weberel/communication-module/tools/tb_export_PCB-test-rig_20260905_1100.csv

ts_ms | ts_utc | key | value
1788560165000 | 2026-09-04 22:16:05 | motion | 0
1788560479000 | 2026-09-04 22:21:19 | motion | 0
1788560671000 | 2026-09-04 22:24:31 | motion | 0
1788560967000 | 2026-09-04 22:29:27 | motion | 0
1788435204000 | 2026-09-03 11:33:24 | reset_reason | 8
1788479013000 | 2026-09-03 23:43:33 | reset_reason | 8
1788522890000 | 2026-09-04 11:54:50 | reset_reason | 8
1788555127000 | 2026-09-04 20:52:07 | reset_reason | 8
1788555490000 | 2026-09-04 20:58:10 | reset_reason | 8
1788557357000 | 2026-09-04 21:29:17 | reset_reason | 11
1788557384000 | 2026-09-04 21:29:44 | reset_reason | 8
1788557638000 | 2026-09-04 21:33:58 | reset_reason | 11
1788558888000 | 2026-09-04 21:54:48 | reset_reason | 11
1788559529000 | 2026-09-04 22:05:29 | reset_reason | 11
1788559864000 | 2026-09-04 22:11:04 | reset_reason | 11
1788560502000 | 2026-09-04 22:21:42 | reset_reason | 11
1788560693000 | 2026-09-04 22:24:53 | reset_reason | 8
1788560986000 | 2026-09-04 22:29:46 | reset_reason | 8
1788598165000 | 2026-09-05 08:49:25 | reset_reason | 8
1788426217000 | 2026-09-03 09:03:37 | solar | 0
1788426521000 | 2026-09-03 09:08:41 | solar | 0
1788426825000 | 2026-09-03 09:13:45 | solar | 0
1788427128000 | 2026-09-03 09:18:48 | solar | 0
1788427432000 | 2026-09-03 09:23:52 | solar | 0
1788427736000 | 2026-09-03 09:28:56 | solar | 0
1788428039000 | 2026-09-03 09:33:59 | solar | 0
1788428343000 | 2026-09-03 09:39:03 | solar | 0
1788428647000 | 2026-09-03 09:44:07 | solar | 0
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
1788550244000 | 2026-09-04 19:30:44 | sensor_ok | 63
1788550547000 | 2026-09-04 19:35:47 | sensor_ok | 63
1788550851000 | 2026-09-04 19:40:51 | sensor_ok | 63
1788551155000 | 2026-09-04 19:45:55 | sensor_ok | 63
1788551458000 | 2026-09-04 19:50:58 | sensor_ok | 63
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
