weberel/communication-module/tools/tb_export_PCB-test-rig_20260906_1107.csv

ts_ms | ts_utc | key | value
1788560165000 | 2026-09-04 22:16:05 | motion | 0
1788560479000 | 2026-09-04 22:21:19 | motion | 0
1788560671000 | 2026-09-04 22:24:31 | motion | 0
1788560967000 | 2026-09-04 22:29:27 | motion | 0
1788561179000 | 2026-09-04 22:32:59 | motion | 1
1788561180000 | 2026-09-04 22:33:00 | motion | 1
1788561181000 | 2026-09-04 22:33:01 | motion | 1
1788561183000 | 2026-09-04 22:33:03 | motion | 1
1788561484000 | 2026-09-04 22:38:04 | motion | 0
1788561785000 | 2026-09-04 22:43:05 | motion | 0
1788562086000 | 2026-09-04 22:48:06 | motion | 0
1788562387000 | 2026-09-04 22:53:07 | motion | 0
1788562688000 | 2026-09-04 22:58:08 | motion | 0
1788562989000 | 2026-09-04 23:03:09 | motion | 0
1788563290000 | 2026-09-04 23:08:10 | motion | 0
1788563590000 | 2026-09-04 23:13:10 | motion | 0
1788563891000 | 2026-09-04 23:18:11 | motion | 0
1788564192000 | 2026-09-04 23:23:12 | motion | 0
1788564493000 | 2026-09-04 23:28:13 | motion | 0
1788564793000 | 2026-09-04 23:33:13 | motion | 0
1788565094000 | 2026-09-04 23:38:14 | motion | 0
1788565395000 | 2026-09-04 23:43:15 | motion | 0
1788565696000 | 2026-09-04 23:48:16 | motion | 0
1788565997000 | 2026-09-04 23:53:17 | motion | 0
1788566297000 | 2026-09-04 23:58:17 | motion | 0
1788566598000 | 2026-09-05 00:03:18 | motion | 0
1788566899000 | 2026-09-05 00:08:19 | motion | 0
1788567200000 | 2026-09-05 00:13:20 | motion | 0
1788567501000 | 2026-09-05 00:18:21 | motion | 0
1788567802000 | 2026-09-05 00:23:22 | motion | 0
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
1788652167000 | 2026-09-05 23:49:27 | solar | 0
1788652469000 | 2026-09-05 23:54:29 | solar | 0
1788652770000 | 2026-09-05 23:59:30 | solar | 0
1788653072000 | 2026-09-06 00:04:32 | solar | 0
1788653373000 | 2026-09-06 00:09:33 | solar | 0
1788653674000 | 2026-09-06 00:14:34 | solar | 0
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
