weberel/communication-module/idf/src/uplink.c

#include "uplink.h"
#include "config.h"
#include "record.h"

#include <string.h>
#include <strings.h>
#include <stdio.h>
#include <stdlib.h>
#include <time.h>
#include <sys/time.h>

#include "esp_log.h"
#include "esp_timer.h"
#include "driver/uart.h"
#include "bq25792.h"
#include "nvs_flash.h"
#include "esp_event.h"
#include "esp_netif.h"
#include "esp_netif_sntp.h"
#include "esp_wifi.h"
#include "esp_http_client.h"
#include "esp_modem_api.h"
#include "mqtt_client.h"
#include "driver/gpio.h"
#include "esp_task_wdt.h"
#include "esp_ota_ops.h"
#include "esp_pm.h"   /* reproduction experiment 2026-09-14 */
#include "freertos/FreeRTOS.h"
#include "freertos/task.h"
#include "freertos/event_groups.h"

#include "board.h"
#include "secrets.h"
#include "gasflow.h"
#include "uss_link.h"
#include "devcfg.h"
#include "ota.h"

#include <math.h>

static const char *TAG = "uplink";

/* Session stopwatch. Zeroed when the modem rail comes up, so every phase
 * number below is directly comparable across sessions and across firmware
 * versions -- and reads as elapsed modem-on time, which is what costs. */
static int64_t s_sess_t0;
static uint32_t sess_ms(void)
{
    return (uint32_t)((esp_timer_get_time() - s_sess_t0) / 1000);
}

/* ISRG Root X1 CA, compiled in from isrg_cert.c (generated from the PEM). */
extern const char isrg_root_pem[];
#define isrg_root_pem_start isrg_root_pem

/* ---- timeouts / policy ---- */
#define MODEM_UART_TX        20
#define MODEM_UART_RX        21

/* Link speed to the A7672.
 *
 * START is what the modem is guaranteed to answer on after a power cycle;
 * AT+IPR is volatile on SIMCom, so every session begins here.
 * FAST is the target once we are talking. 921600 needs R405-R408 at 2.2 k --
 * with the stock 10 k level-shifter pull-ups 230400 is the ceiling and 460800
 * is dead (testing-status.md). Lower FAST to 230400 on an un-reworked board. */
/* Upper bound on how long we wait for the modem to answer AT after PWRKEY.
 * Generous on purpose -- this is a ceiling, not a delay: the poll exits as soon
 * as the modem replies, so a slow boot costs only what it actually costs. */
#define MODEM_READY_TO_MS    15000

#define MODEM_BAUD_START     115200
/* DISABLED (set equal to START) after a measured failure, 2026-09-21.
 *
 * TRIED: 921600, which testing-status.md says this unit's reworked 2.2 k
 * level-shifter pull-ups support. RESULT: "did not stick", and the session then
 * failed at REGISTRATION (reg=0) having burned 37.6 s.
 *
 * WHY THE FALLBACK BELOW CANNOT WORK. AT+IPR SUCCEEDS -- the modem moves to the
 * new rate. If our own re-sync then fails, dropping our UART back to 115200
 * leaves the modem at 921600, i.e. mismatched in the one direction that cannot
 * be talked out of: commanding it back needs the link that is broken. Only a
 * rail power-cycle recovers it, which is why the whole session was lost.
 *
 * AND IT WAS NEVER THE BOTTLENECK. One batch is 8 records ~7 KB = 0.6 s at
 * 115200, yet the measured failure was n_batch=0 with an 18.4 s drain: the
 * first publish transmitted fine and then waited for an ACK that never came.
 * The session's cost is TIMEOUTS (publish 20 s, reconnect 15 s, teardown 18.5 s,
 * modem boot 8.9 s), not throughput. Raise this only with a re-sync that is
 * retried at BOTH rates before giving up, and only if throughput is ever shown
 * to bind. */
#define MODEM_BAUD_FAST      115200
#define ATTACH_TIMEOUT_S     45      /* normal attach budget */
#define ATTACH_DEEP_S        180     /* once-a-day deep search */
#define NO_SIGNAL_FAILFAST_S 25      /* CSQ still 99 after this -> abort attempt */
#define MQTT_CONNECT_TO_MS   30000
#define PUBLISH_TO_MS        20000
/* Back to 8 after the telemetry trim: 22 datapoints per record x 8 = ~176 per
 * publish, comfortably under what made ThingsBoard Cloud drop the connection
 * (that was ~320, at 40 datapoints x 8). Larger batches drain a backlog in
 * fewer round trips, which matters over a slow cellular link. */
#define BATCH_RECORDS        8
#define BATCH_GAP_MS         400     /* ThingsBoard Cloud dislikes bursts */

#define CLOCK_MIN 1767225600L        /* 2026-01-01 */
#define CLOCK_MAX 2082758400L        /* 2036-01-01 */

static bool clock_valid(void)
{
    time_t t = time(NULL);
    return t >= CLOCK_MIN && t < CLOCK_MAX;
}

/* ===================== MQTT publisher (transport-agnostic) ===================== */

static EventGroupHandle_t s_ev;
#define EV_MQTT_UP   BIT0
#define EV_MQTT_FAIL BIT1
#define EV_PUBACK    BIT2
#define EV_IP_UP     BIT3
#define EV_CFG_DONE  BIT4   /* config topic answered: payload, or the subscribe was refused */

static esp_mqtt_client_handle_t s_mqtt;
static volatile int s_pending_msg_id = -1;

/* ---- downlink: retained config (com-0.35, DOWNLINK.md) ----------------------
 * The device may only READ ecotrace/<user>/config; the ACL refuses everything
 * else, and until the ACL is deployed the SUBSCRIBE itself is refused. Both
 * are "no config", not errors. */
#define MQTT_CFG_TOPIC   "ecotrace/" MQTT_USERNAME "/config"
#define CFG_WAIT_MS      2000      /* retained delivery follows SUBACK at once;
                                    * the wait only runs out when nothing is retained */
static volatile int s_cfg_sub_id = -1;
static volatile devcfg_rc_t s_cfg_rc;
static volatile bool s_cfg_seen;    /* a payload arrived this session */

static void mqtt_event(void *arg, esp_event_base_t base, int32_t id, void *data)
{
    esp_mqtt_event_handle_t e = data;
    switch ((esp_mqtt_event_id_t)id) {
    case MQTT_EVENT_CONNECTED:    xEventGroupSetBits(s_ev, EV_MQTT_UP);   break;
    case MQTT_EVENT_ERROR:
    case MQTT_EVENT_DISCONNECTED: xEventGroupSetBits(s_ev, EV_MQTT_FAIL); break;
    case MQTT_EVENT_PUBLISHED:
        if (e->msg_id == s_pending_msg_id) xEventGroupSetBits(s_ev, EV_PUBACK);
        break;
    case MQTT_EVENT_SUBSCRIBED:
        if (e->msg_id == s_cfg_sub_id && e->error_handle &&
            e->error_handle->error_type == MQTT_ERROR_TYPE_SUBSCRIBE_FAILED) {
            /* MQTT 5 reason code >= 0x80: not authorised (ACL not deployed
             * yet). Same as an empty topic. */
            ESP_LOGW(TAG, "config subscribe refused -- no config");
            xEventGroupSetBits(s_ev, EV_CFG_DONE);
        }
        break;
    case MQTT_EVENT_DATA:
        if (e->topic_len == (int)strlen(MQTT_CFG_TOPIC) &&
            memcmp(e->topic, MQTT_CFG_TOPIC, e->topic_len) == 0) {
            /* Payloads are a few hundred bytes, far below the client's
             * buffer, so one event carries the whole message; anything that
             * arrives fragmented is not a config we know and is dropped. */
            if (e->current_data_offset == 0 && e->total_data_len == e->data_len) {
                s_cfg_rc   = devcfg_apply(e->data, (size_t)e->data_len);
                s_cfg_seen = true;
                xEventGroupSetBits(s_ev, EV_CFG_DONE);
            }
        }
        break;
    default: break;
    }
}

static bool mqtt_up(void)
{
    esp_mqtt_client_config_t cfg = {
        .broker.address.uri = MQTT_URI,
        /* PINNED, do not touch. Let's Encrypt moved to the Generation Y root in
         * Jan 2026, so certs now chain to ISRG Root YR -- the SERVER is
         * configured to serve the chain cross-signed by X1 precisely so this
         * file keeps working. X1 is being retired eventually; pin Root YR (or
         * both) then, not now. */
        .broker.verification.certificate = isrg_root_pem_start,
        .credentials.username = MQTT_USERNAME,
        /* The secret goes in the PASSWORD field, not the username: brokers log
         * usernames on every connect. */
        .credentials.authentication.password = MQTT_PASSWORD,
        /* MQTT 5, and this is not cosmetic. On 3.1.1 a broker that REFUSES a
         * publish still returns PUBACK -- there is no not-authorised code --
         * and publish_acked() advances the flash ring cursor on PUBACK. A
         * refused publish would therefore discard records that never arrived.
         * MQTT 5 returns reason code 0x87 and the refusal becomes visible. */
        .session.protocol_ver = MQTT_PROTOCOL_V_5,
        .network.timeout_ms = 15000,
        .session.keepalive = 60,
    };
    s_mqtt = esp_mqtt_client_init(&cfg);
    if (!s_mqtt) return false;
    esp_mqtt_client_register_event(s_mqtt, ESP_EVENT_ANY_ID, mqtt_event, NULL);
    xEventGroupClearBits(s_ev, EV_MQTT_UP | EV_MQTT_FAIL);
    if (esp_mqtt_client_start(s_mqtt) != ESP_OK) return false;
    EventBits_t b = xEventGroupWaitBits(s_ev, EV_MQTT_UP | EV_MQTT_FAIL,
                                        pdTRUE, pdFALSE,
                                        pdMS_TO_TICKS(MQTT_CONNECT_TO_MS));
    return (b & EV_MQTT_UP) != 0;
}

static void mqtt_down(void)
{
    if (!s_mqtt) return;
    esp_mqtt_client_stop(s_mqtt);
    esp_mqtt_client_destroy(s_mqtt);
    s_mqtt = NULL;
}

/* Subscribe to the retained config and wait for it, at most CFG_WAIT_MS.
 * Runs BEFORE the drain so the sleep length and upload countdown computed
 * after the session already use the new values (the ack in the status
 * message is then what will actually happen). Nothing here can fail the
 * session: no payload, a refused subscribe or a rejected payload all leave
 * the NVS values in force. */
static void config_fetch(void)
{
    if (!s_mqtt) return;
    s_cfg_seen = false;
    xEventGroupClearBits(s_ev, EV_CFG_DONE);
    s_cfg_sub_id = esp_mqtt_client_subscribe(s_mqtt, MQTT_CFG_TOPIC, 1);
    if (s_cfg_sub_id < 0) { ESP_LOGW(TAG, "config subscribe not sent"); return; }
    EventBits_t b = xEventGroupWaitBits(s_ev, EV_CFG_DONE, pdTRUE, pdFALSE,
                                        pdMS_TO_TICKS(CFG_WAIT_MS));
    if (!(b & EV_CFG_DONE))
        ESP_LOGI(TAG, "no retained config within %d ms", CFG_WAIT_MS);
    else if (s_cfg_seen)
        ESP_LOGI(TAG, "config: %s (ver %lu, sample %lu s, upload %lu s)",
                 devcfg_rc_name(s_cfg_rc), (unsigned long)devcfg_ver(),
                 (unsigned long)devcfg_sample_s(), (unsigned long)devcfg_upload_s());
    esp_mqtt_client_unsubscribe(s_mqtt, MQTT_CFG_TOPIC);
}

/* ---- OTA (com-0.36, DOWNLINK.md "OTA semantics") --------------------------
 * After the drain, so the data always goes first, and before the status
 * message, so a failure is reported in the same session. On success the
 * status still carries the OLD version (the new image's first session is the
 * acknowledgement) and main.c restarts once the session is torn down.
 *
 * Only tried with a comfortable battery: the new image must complete one
 * upload session before its first deep sleep or the bootloader rolls it back,
 * and a session that is skipped for a low pack would waste the whole attempt. */
#define OTA_MIN_VBAT_MV   (MODEM_MIN_VBAT_MV + 100)
#define OTA_MAX_TRIES     3

/* This session published, so the image that is running works: tell the
 * bootloader to keep it. MUST run before ota_attempt(), and nowhere after it:
 * esp_ota_mark_app_valid_cancel_rollback() marks whichever otadata entry is
 * ACTIVE, not the partition that is running, and esp_https_ota_finish() makes
 * the freshly written slot the active entry. Marking after an OTA therefore
 * validates the NEW image before it has ever booted, and the bootloader will
 * never roll it back (found 2026-10-01: a build with a wrong broker host
 * survived every wake; the four OTAs the day before had no protection either).
 * A no-op unless this slot is PENDING_VERIFY, i.e. our own first boot after
 * an OTA. */
static void confirm_running_image(const uplink_result_t *res)
{
    if (!res->any_success) return;
    const esp_partition_t *run = esp_ota_get_running_partition();
    esp_ota_img_states_t st;
    if (run && esp_ota_get_state_partition(run, &st) == ESP_OK && st == ESP_OTA_IMG_PENDING_VERIFY) {
        esp_ota_mark_app_valid_cancel_rollback();
        ESP_LOGI(TAG, "first session after OTA published -- %s (" FW_VERSION ") marked valid", run->label);
    }
}

static void ota_attempt(const uplink_ctx_t *ctx, uplink_result_t *res)
{
    confirm_running_image(res);
    const devcfg_fw_t *t = devcfg_fw_target();
    if (!t || res->ota_ready) return;
    if (strcmp(t->ver, FW_VERSION) == 0) return;          /* already running it */
    if (ctx->vbat_mv && ctx->vbat_mv < OTA_MIN_VBAT_MV) {
        ESP_LOGW(TAG, "OTA %s deferred: VBAT %u mV < %d", t->ver, ctx->vbat_mv, OTA_MIN_VBAT_MV);
        return;
    }
    uint8_t n = devcfg_fw_tries(t->ver);
    if (n >= OTA_MAX_TRIES) {
        ESP_LOGW(TAG, "OTA %s not retried (%u attempts)", t->ver, n);
        return;
    }
    /* A version that downloaded, booted and then could not upload was rolled
     * back by the bootloader: the same bytes would fail the same way, and a
     * retry here would run BEFORE the status message and clear the very
     * fw_err the server needs to see. Stricter than the contract's three
     * attempts, on purpose. A different fw_ver lifts it. */
    if (devcfg_fw_err() && strcmp(devcfg_fw_err(), "rollback") == 0 &&
        devcfg_fw_err_ver() && strcmp(devcfg_fw_err_ver(), t->ver) == 0) {
        ESP_LOGW(TAG, "OTA %s not retried: it was rolled back", t->ver);
        return;
    }
    devcfg_fw_note_try(t->ver);                            /* counted before, so a crash counts */
    esp_task_wdt_reset();
    ota_rc_t rc = ota_run(t->ver, t->url, t->sha256);
    if (rc == OTA_OK) {
        devcfg_fw_clear_err();
        res->ota_ready = true;
    } else {
        devcfg_fw_set_err(ota_rc_name(rc), t->ver);
    }
}

/* QoS 1 publish, blocking until PUBACK -- the ring cursor only advances on ack. */
static bool publish_acked(const char *json)
{
    if (!s_mqtt) return false;
    xEventGroupClearBits(s_ev, EV_PUBACK | EV_MQTT_FAIL);
    /* Per-device topic. The broker ACL is `pattern write ecotrace/%u/telemetry`,
     * so this must match the authenticated username or the publish is refused
     * -- visibly, now that we speak MQTT 5. */
    int id = esp_mqtt_client_publish(s_mqtt, MQTT_TOPIC, json, 0, 1, 0);
    if (id < 0) return false;
    s_pending_msg_id = id;
    EventBits_t b = xEventGroupWaitBits(s_ev, EV_PUBACK | EV_MQTT_FAIL,
                                        pdTRUE, pdFALSE,
                                        pdMS_TO_TICKS(PUBLISH_TO_MS));
    return (b & EV_PUBACK) != 0;
}

/* ---- derived ultrasonic values (gasflow.c) ---------------------------------
 *
 * The server does not compute (agreed 2026-09-25), so the board sends the
 * derived set it plots: per sample c, CH4 fraction and the 0/1 flags; per
 * window the gas and METHANE volumes at standard conditions, mean flow, Re,
 * cutoff, coverage and length. The raw keys still carry every input, so a
 * refit can recompute history later; uss_derive_ver names the constants.
 * (idf-0.31 had cut this to methane only; the server asked for the rest back
 * in 0.32/0.33.)
 *
 * Computed HERE, at upload, from the raw fields already in the record, so the
 * record layout (and REC_MAGIC) stays untouched and a backlog logged before
 * this build still gets it.
 *
 * WINDOWS come from a record and its PREDECESSOR in the flash ring, read back
 * by seq -- not remembered in RAM, so it survives deep sleep, reboots and
 * sessions that start mid-backlog alike. No predecessor, no window: a missing
 * predecessor is never treated as zero. */
static void raw_of(const LogRecord *r, gf_raw_t *raw)
{
    raw->code        = r->uss_code;
    raw->tof_ups_q40 = r->uss_tof_ups_q40;
    raw->tof_dns_q40 = r->uss_tof_dns_q40;
    raw->dtof_ps     = r->uss_dtof_ps;
    raw->amp_ups     = r->uss_amp_ups;
    raw->amp_dns     = r->uss_amp_dns;
    raw->gain        = r->uss_gain;
}

/* A sample needs the module (bit 4) AND the in-line MS5837 (bit 3). */
static void sample_of(const gf_cfg_t *cfg, const LogRecord *r, gf_sample_t *s)
{
    gf_raw_t raw;
    memset(s, 0, sizeof(*s));
    if ((r->sensor_ok & 0x18) != 0x18) return;
    raw_of(r, &raw);
    gf_sample(cfg, &raw, r->press_dmbar / 10.0, r->temp_cC / 100.0, s);
}

/* Window between prev and cur. Returns NULL and fills *w on success, or a short
 * reason, which is published so a missing volume explains itself. */
static const char *window_of(const gf_cfg_t *cfg, const LogRecord *prev,
                             const LogRecord *cur, const gf_sample_t *s_cur,
                             gf_window_t *w, double *cov, uint32_t *dt_s)
{
    if (!(prev->sensor_ok & 0x10) || !(cur->sensor_ok & 0x10)) return "no_module";
    if (cur->uss_tot_flags & USS_TOT_FLAG_SAT)                 return "saturated";
    /* <= 0 also covers a totalizer reset and pre-PROTO 3 records (all zero). */
    int64_t ds0 = cur->uss_s0 - prev->uss_s0;
    int64_t ds1 = cur->uss_s1 - prev->uss_s1;
    if (ds0 <= 0)                                              return "ds0";

    /* Wall-clock window. uptime_s is only comparable within one boot epoch. */
    if (prev->ts_s && cur->ts_s > prev->ts_s)
        *dt_s = cur->ts_s - prev->ts_s;
    else if (prev->boot_id == cur->boot_id && cur->uptime_s > prev->uptime_s)
        *dt_s = cur->uptime_s - prev->uptime_s;
    else                                                       return "no_dt";

    /* Composition, P and T from this record's sample, else the predecessor's
     * (the window touches both ends). */
    gf_sample_t s_prev;
    const gf_sample_t *rep = s_cur;
    const LogRecord   *rr  = cur;
    if (!rep->ok) {
        sample_of(cfg, prev, &s_prev);
        rep = &s_prev;
        rr  = prev;
    }
    /* Kept apart on purpose: without the in-line MS5837 there is no pressure
     * or temperature, so the volume cannot be taken to standard conditions and
     * -- worse -- the CH4 fraction cannot be read from the speed of sound at
     * all (it needs the gas temperature). That is a missing sensor, not a bad
     * ultrasonic sample, and the two need different fixes. */
    if (!rep->ok && !(cur->sensor_ok & 0x08) && !(prev->sensor_ok & 0x08))
                                                               return "no_pt";
    if (!rep->ok)                                              return "no_sample";

    /* Integrated time claimed by S0, at the representative ToF, against the
     * wall clock. Above 1 means the sum claims more time than passed. Median
     * 0.990 over a day of field windows (eco-field-02, 2026-09-23).
     *
     * Not judged below 60 s: record stamps are whole seconds and are taken a
     * few seconds before the totalizer read, which alone moves a 5 s window's
     * coverage by +-50 %. The volume of a short window does not depend on dt,
     * so it is kept rather than thrown away on a check it cannot pass. */
    double tu_ns = rr->uss_tof_ups_q40 / 1099511.627776 * 1000.0;
    double td_ns = rr->uss_tof_dns_q40 / 1099511.627776 * 1000.0;
    *cov = (double) ds0 / 1099511627776.0 * tu_ns * td_ns / (*dt_s * 1000.0);
    if (*dt_s >= 60 && *cov > USS_WIN_COV_MAX)                return "coverage";

    if (!gf_window(cfg, ds1, ds0, *dt_s * 1000u, rep, w))     return "window";
    if (fabs(w->q_n_lpm) > USS_WIN_Q_MAX_LPM)                  return "q_max";
    return NULL;
}

static int derived_values(const LogRecord *r, char *out, size_t cap)
{
    gf_cfg_t cfg;
    gf_profile(&cfg, USS_GAS_PROFILE, USS_CELL);

    gf_sample_t s;
    sample_of(&cfg, r, &s);

    /* Configuration: what the server needs to recompute from the raw keys.
     * uss_validated is a property of profile + cell (always 0 on 44 mm): it is
     * what marks provisional data, so it goes on every record. */
    int n = snprintf(out, cap,
        ",\"uss_gas\":\"%s\",\"uss_cell\":%d,\"uss_derive_ver\":%d,\"uss_validated\":%u",
        gf_gas_name(cfg.kind), gf_cell_mm(cfg.cell), GF_DERIVE_VER,
        cfg.validated ? 1u : 0u);
    if (n < 0 || (size_t)n >= cap) return -1;

    /* Sample flags, sent as 0 OR 1 whenever the check actually ran, so an
     * absent key means "not evaluated", never "not set" (server request,
     * 2026-09-25). The ToF check runs on every code-122 sample with P and T;
     * the composition and the echo check only on one whose ToF passed. A
     * record without them says why through uss_code / sensor_ok. */
    if (s.ok || s.tof_bad)
        n += snprintf(out + n, cap - n, ",\"uss_tof_bad\":%u", s.tof_bad ? 1u : 0u);
    if (s.ok && n > 0 && (size_t)n < cap)
        n += snprintf(out + n, cap - n,
                      ",\"uss_c_mps\":%.2f,\"uss_x_a\":%.4f,\"uss_not_gas\":%u",
                      s.c_mps, s.x_a, s.not_gas ? 1u : 0u);
    if (n < 0 || (size_t)n >= cap) return -1;

    LogRecord prev;
    if (r->seq == 0 || !flashlog_read_seq(r->seq - 1, &prev))
        return n + snprintf(out + n, cap - n, ",\"uss_win_err\":\"no_prev\"");

    gf_window_t w;
    double   cov  = 0.0;
    uint32_t dt_s = 0;
    const char *err = window_of(&cfg, &prev, r, &s, &w, &cov, &dt_s);
    if (err)
        return n + snprintf(out + n, cap - n, ",\"uss_win_err\":\"%s\"", err);

    /* Standard litres (20 C, 1013.25 mbar) in the window since the previous
     * record: total volume from the totalizer, taken to standard conditions
     * with the in-line P and T. Both 0 below the low-flow cutoff.
     * uss_v_ch4_std_l is that times the CH4 fraction from the speed of sound,
     * and 0 when the echo says the line does not hold biogas at all. "Methane"
     * only means something under the biogas profile, where the profile's first
     * component IS CH4, so for air/N2 only the total goes out. */
    n += snprintf(out + n, cap - n,
        ",\"uss_v_std_l\":%.4f,\"uss_q_std_lpm\":%.3f,\"uss_re\":%.0f,\"uss_cut\":%u,"
        "\"uss_cov\":%.3f,\"uss_win_s\":%lu",
        w.v_n_ul / 1e6, w.q_n_lpm, w.re, w.cut ? 1u : 0u, cov, (unsigned long) dt_s);
    if (cfg.kind == GF_GAS_BIOGAS && n > 0 && (size_t)n < cap)
        n += snprintf(out + n, cap - n, ",\"uss_v_ch4_std_l\":%.4f", w.v_a_n_ul / 1e6);
    return n;
}

/* ---- ThingsBoard JSON, same schema the dashboards already use ---- */

/* Returns the length written, or -1 if the payload did not fit. A truncated
 * record is worse than no record: it produces malformed JSON that takes the
 * whole batch down with it. */
static int record_values(const LogRecord *r, char *out, size_t cap)
{
    /* TRIMMED SET (2026-08-15): ~40 datapoints -> 22.
     *
     * Rule applied: publish what you would act on or analyse. Drop what is
     * derivable from other fields, what is only wanted for a post-mortem, and
     * what is structurally constant. Nothing is actually lost -- the 128-byte
     * flash record still carries every field, so a unit can be interrogated
     * after the fact; this only trims what crosses the air.
     *
     * Dropped and why:
     *   bat_mw                 = vbat * ibat, derivable
     *   vac2_mv, vsys_mv,
     *   vreg_mv, vindpm_mv     charger internals; post-mortem, not decisions
     *   fault0, fault1         almost always 0; the record keeps them
     *   weather_good, eco_chg  derived heuristics, recomputable from harvest
     *   light_ch1              IR channel; ch0 is the one that means anything
     *   press_mbar             DUPLICATE of p_gas_hpa (same MS5837 reading)
     *   tdie_c, ts_pct,
     *   ts_stat                charger thermal diagnostics
     *   flow_lpm               VFR constants are wrong for this cell; it is a
     *                          misleading number until the lab calibration
     *   uss_amp_ups/dns, gain  summarised by uss_snr_db (a degrading signal
     *                          shows up there); the record keeps the detail
     *   uss_status             AUTO/BOOT bits; vol_ml resetting says the same
     *   p_atm_hpa, is_const    a compile-time constant, same every sample
     *   wf_praw, wf_traw       the WF280A does not produce usable data
     *
     * uss_tof_us is the MEAN of the two directions, not both. That is the
     * principled split: the mean is the speed-of-sound (composition) signal,
     * and the difference is the flow signal, which uss_dtof_us already carries
     * at far better resolution. Publishing both directions separately sent the
     * same information twice. */
    /* Provenance first (com-0.34, server request 2026-09-30): seq is the flash
     * ring cursor the record was written at -- recovered from the journal and
     * a forward scan on every cold boot, so it never restarts at zero and is
     * contiguous within a boot_id. A hole in seq is a record that was lost or
     * overwritten by the ring, never a numbering artefact. boot_id is the
     * 8-bit random stamp of the cold boot that wrote it, the same value the
     * status message carries. */
    int n = snprintf(out, cap,
        "\"seq\":%lu,\"boot_id\":%u,"
        "\"vbat_mv\":%u,\"ibat_ma\":%d,\"soc_pct\":%u,"
        "\"vbus_mv\":%u,\"ibus_ma\":%d,\"chg_stat\":%u,"
        "\"harvest_mah\":%u,\"solar\":%u,\"usb\":%u,"
        "\"light_ch0\":%u,"
        "\"acc_x_mg\":%d,\"acc_y_mg\":%d,\"acc_z_mg\":%d,"
        "\"temp_c\":%.2f,\"sensor_ok\":%u",
        (unsigned long)r->seq, r->boot_id,
        r->vbat_mv, r->ibat_ma, r->soc_pct,
        r->vbus_mv, r->ibus_ma, r->chg_stat,
        r->harvest_mah,
        (r->flags & RECF_SOLAR) ? 1 : 0, (r->flags & RECF_USB) ? 1 : 0,
        r->light_ch0,
        r->acc_mg[0], r->acc_mg[1], r->acc_mg[2],
        r->temp_cC / 100.0f, r->sensor_ok);

    /* Supply and charger faults. Restored to telemetry 2026-09-22: these are
     * read into every record already, but the 2026-08-15 trim dropped them to
     * fit a ThingsBoard datapoint limit we no longer have. VSYS is the rail the
     * ESP32 and the module actually brown out on -- without it every reset
     * analysis is inferred from VBAT, which is the wrong node. */
    if (n > 0 && (size_t)n < cap)
        n += snprintf(out + n, cap - n,
            ",\"vsys_mv\":%u,\"fault0\":%u,\"fault1\":%u",
            r->vsys_mv, r->fault0, r->fault1);

    /* Ultrasonic: four core values plus SNR as the health indicator. Only when
     * the module answered, so boards without a gas cell burn no quota. */
    if ((r->sensor_ok & 0x10) && n > 0 && (size_t)n < cap) {
        double tof_us = (r->uss_tof_ups_q40 / 1099511.627776 +
                         r->uss_tof_dns_q40 / 1099511.627776) / 2.0;
        n += snprintf(out + n, cap - n,
            ",\"uss_tof_us\":%.4f,\"uss_dtof_us\":%.6f,"
            "\"uss_code\":%u,\"uss_snr_db\":%.1f,\"uss_vol_ml\":%lu,\"uss_seq\":%d,\"uss_recov\":%u"
            /* RAW TOTALIZER, restored 2026-09-22 now that the module runs
             * PROTO 3 (before that these were identically zero, and the link
             * was hitting a ThingsBoard datapoint throttle that no longer
             * exists).
             *
             * ABSOLUTE running sums, not per-record deltas: diff them
             * server-side to get a window, which is what makes a dropped
             * uplink cost nothing. These are the numbers calibration is fitted
             * against, and the only ones that stay correct when K or the zero
             * offset is changed later -- see the derivation in uss_link.h.
             * Both stay well inside 2^53, so JSON carries them exactly; S0 is
             * the faster of the two at ~3.5e12 per year. */
            ",\"uss_s1\":%lld,\"uss_s0\":%lld,\"uss_skip\":%u"
            /* Echo amplitudes and PGA gain, restored 2026-09-25 (the 08-15 trim
             * dropped them). They are the "is it this gas at all?" input: air
             * in a biogas line reads ~61 % CH4 by speed of sound alone and only
             * the echo strength gives it away. uss_not_gas below is the
             * device's verdict; these let the server re-judge it. */
            ",\"uss_amp_ups\":%u,\"uss_amp_dns\":%u,\"uss_gain\":%u",
            tof_us, r->uss_dtof_ps / 1e6f,
            r->uss_code, r->uss_snr_db2 / 2.0f,
            (unsigned long)r->uss_vol_ml,
            /* 0xFFFF = logged before this field existed */
            r->uss_seq == 0xFFFFu ? -1 : (int) r->uss_seq,
            r->uss_recoveries,
            (long long) r->uss_s1, (long long) r->uss_s0, r->uss_tot_skip,
            r->uss_amp_ups, r->uss_amp_dns, r->uss_gain);
        /* uss_vol_ml above is LEGACY: the module's VOL_ML integrator still
         * carries the old 44 mm cell's constants and is wrong for the 75 mm
         * cell. Kept only because the server reads the key. uss_v_std_l is the
         * volume to use. */
        if (n > 0 && (size_t)n < cap) {
            int d = derived_values(r, out + n, cap - n);
            n = (d < 0) ? -1 : n + d;
        }
    }

    /* Gas pressure from the MS5837 (it sits in the LINE, not ambient), and the
     * differential against the per-site atmospheric constant in config.h. */
    if ((r->sensor_ok & 0x08) && n > 0 && (size_t)n < cap) {
        float p_gas = r->press_dmbar / 10.0f;
        n += snprintf(out + n, cap - n,
            ",\"p_gas_hpa\":%.2f,\"dp_hpa\":%.2f",
            p_gas, p_gas - P_ATM_CONST_HPA);
    }

    /* snprintf returns what it WOULD have written, so n > cap means we lost
     * bytes somewhere above. Say so rather than emitting broken JSON. */
    if (n < 0 || (size_t)n >= cap) return -1;
    return n;
}

/* 16 KB: 8 records at ~1.5 KB each with the derived ultrasonic keys. 10 KB no
 * longer held a full batch. */
static char s_json[16384];

/* Reference for back-dating: the uptime and boot epoch of the newest record
 * (set from the ctx at the start of every session). */
static uint32_t s_ref_uptime_s;
static uint8_t  s_ref_boot_id;

/* Timestamp for one record.
 *
 * A record logged before the first clock sync carries ts_s = 0 and has to be
 * placed in time at upload. Doing that from its ring position assumes every
 * wake was exactly SAMPLE_INTERVAL_S apart -- which is false in precisely the
 * situations a clockless device is in: critical-battery mode (x6), park mode
 * (3600 s), button wakes and crash reboots. uptime_s is monotonic elapsed time
 * and carries no such assumption, so it goes first.
 *
 * It is only meaningful within one boot epoch (a cold boot restarts uptime at
 * 0 and rolls boot_id), so records from an older epoch keep the position
 * estimate as a last resort -- coarse, but better than a timestamp built on an
 * uptime that has since restarted.
 *
 * Both branches anchor at now_ms, so everything is late by however long this
 * session has been running (minutes at worst); the alternative is baking the
 * session duration into the reference, which buys little and can go negative. */
static int64_t record_ts_ms(const LogRecord *r, int64_t now_ms, uint32_t head)
{
    if (r->ts_s) return (int64_t)r->ts_s * 1000;
    if (r->boot_id == s_ref_boot_id && r->uptime_s <= s_ref_uptime_s)
        return now_ms - (int64_t)(s_ref_uptime_s - r->uptime_s) * 1000;
    return now_ms - (int64_t)(head - 1 - r->seq) * devcfg_sample_s() * 1000;
}

static uint32_t drain(uplink_result_t *res)
{
    uint32_t sent = 0;
    while (flashlog_pending() > 0) {
        int64_t t_batch = esp_timer_get_time();

        /* Power doc B2: sample the supply WHILE the modem is transmitting.
         *
         * Taken on the second batch, not the first: by then the link is warm
         * and we are actually pushing data, whereas the first publish can
         * complete before the radio has drawn anything worth measuring. One
         * sample only -- this is a diagnostic, and the I2C read itself costs
         * session time we just spent effort removing. */
        if (res->n_batches == 1 && res->vsys_load_mv == 0) {
            res->vbat_load_mv = bq_vbat_mv();
            res->vsys_load_mv = bq_vsys_mv();
            bq_faults(&res->fault0, &res->fault1);
            ESP_LOGW(TAG, "under load: vbat %u mV, vsys %u mV (idle vbat %u) "
                          "| drop %d mV, fault %02x/%02x",
                     res->vbat_load_mv, res->vsys_load_mv, res->vbat_pre_mv,
                     (int) res->vbat_pre_mv - (int) res->vbat_load_mv,
                     res->fault0, res->fault1);
        }
        esp_task_wdt_reset();
        int64_t now_ms = clock_valid() ? (int64_t)time(NULL) * 1000 : 0;
        uint32_t n = flashlog_pending();
        if (n > BATCH_RECORDS) n = BATCH_RECORDS;

        size_t len = 0;
        uint32_t included = 0;
        s_json[len++] = '[';
        for (uint32_t i = 0; i < n; i++) {
            LogRecord r;
            if (!flashlog_peek(i, &r)) continue;
            /* 1536, not 800: the record payload is ~1070 chars now (28 base
             * fields + 9 USS + 4 ToF, two of them 9-digit Q40 integers + 4
             * pressure + 2 WF280A). At 800 it truncated mid-field, the JSON
             * came out malformed, and ThingsBoard silently rejected the whole
             * batch -- the symptom was every sensor key frozen while the
             * separate (short) status payload kept updating. */
            /* STATIC, not on the stack. The main task stack is 4 KB and a
             * 1536-byte automatic here overflowed it -- ESP-IDF caught it as a
             * stack protection fault mid-upload, so the device rebooted every
             * cycle and never sent anything. Static is safe: this loop is
             * single-threaded and the buffer is consumed before the next pass. */
            static char vals[1536];
            if (record_values(&r, vals, sizeof(vals)) < 0) {
                ESP_LOGE(TAG, "record payload truncated -- telemetry dropped");
                continue;
            }
            int w;
            if (now_ms > 0)
                w = snprintf(s_json + len, sizeof(s_json) - len - 2,
                             "%s{\"ts\":%lld,\"values\":{%s}}",
                             included ? "," : "",
                             (long long)record_ts_ms(&r, now_ms, flashlog_head_seq()),
                             vals);
            else
                w = snprintf(s_json + len, sizeof(s_json) - len - 2,
                             "%s{%s}", included ? "," : "", vals);
            /* Batch full: stop HERE and consume only what was processed. The
             * advance below used to take the full n regardless, so the records
             * that did not fit were marked sent without ever leaving the board. */
            if (w < 0 || (size_t)w >= sizeof(s_json) - len - 2) { n = i; break; }
            len += (size_t)w;
            included++;
        }
        s_json[len++] = ']';
        s_json[len] = 0;

        if (included == 0) { flashlog_advance(n); continue; }
        if (!publish_acked(s_json)) {
            /* Broker churn (TB Cloud drops the connection every ~18 s during
             * drains): wait out the client's auto-reconnect, then retry --
             * turns a stopped drain into a slightly slower one. */
            esp_task_wdt_reset();
            xEventGroupWaitBits(s_ev, EV_MQTT_UP, pdTRUE, pdFALSE,
                                pdMS_TO_TICKS(15000));
            esp_task_wdt_reset();
            if (!publish_acked(s_json)) {
                ESP_LOGW(TAG, "drain stopped at batch %u, %lu pending, "
                              "%lu ms into the session",
                         res->n_batches, (unsigned long)flashlog_pending(),
                         (unsigned long)sess_ms());
                res->drain_broke = true;
                break;
            }
        }
        flashlog_advance(n);
        sent += included;
        {
            uint32_t dt = (uint32_t)((esp_timer_get_time() - t_batch) / 1000);
            if (dt > res->t_pub_max_ms) res->t_pub_max_ms = dt;
            res->n_batches++;
        }
        if (flashlog_pending() > 0) vTaskDelay(pdMS_TO_TICKS(BATCH_GAP_MS));
    }
    return sent;
}

/* QoS-1 publish that survives broker churn: on failure wait out the client's
 * auto-reconnect, then retry once (2026-08-13 audit: the status record was
 * being eaten by the end-of-session disconnect nearly every time). */
static bool publish_resilient(const char *json)
{
    if (publish_acked(json)) return true;
    esp_task_wdt_reset();
    xEventGroupWaitBits(s_ev, EV_MQTT_UP, pdTRUE, pdFALSE, pdMS_TO_TICKS(15000));
    esp_task_wdt_reset();
    return publish_acked(json);
}

static void send_status(const uplink_ctx_t *ctx, const uplink_result_t *res)
{
    const char *transport = (res->sent && res->used_wifi) ? "wifi" :
                            res->sent ? "cell" : "none";
    int64_t now_ms = clock_valid() ? (int64_t)time(NULL) * 1000 : 0;
    static char vals[1024];         /* keep it off the 4 KB main stack too */
    snprintf(vals, sizeof(vals),
             "\"rssi_dbm\":%d,\"wifi_rssi_dbm\":%d,\"transport\":\"%s\","
             "\"cereg_stat\":%u,\"backlog\":%lu,\"boot_id\":%u,"
             /* Why this session ran (com-0.34): reset_reason cannot tell a
              * button press from a timer wake, and crash_count only counts. */
             "\"reset_reason\":%u,\"wake_reason\":\"%s\","
             "\"boot_count\":%u,\"wake_count\":%u,"
             "\"crash_count\":%u,\"vbat_mv\":%u,"
             "\"sun_h\":%u,\"voc_max_mv\":%u,\"fw\":\"" FW_VERSION "\","
             "\"uss_rst_cause\":%d,\"uss_lh_starts\":%d,\"uss_lh_uptime\":%d,"
             "\"uss_preset\":%d,"
             /* Session phase timing. Cumulative ms of modem-on time; a phase's
              * own cost is the difference from the previous column. */
             "\"t_modem\":%lu,\"t_reg\":%lu,\"t_ppp\":%lu,\"t_sntp\":%lu,"
             "\"t_mqtt\":%lu,\"t_drain\":%lu,\"t_pubmax\":%lu,"
             "\"n_batch\":%u,\"n_sent\":%lu,\"drain_broke\":%u,"
             /* Supply under load -- see power doc B2. vbat_pre is with the
              * modem off; the difference is the sag that sets battery sizing. */
             "\"vbat_pre\":%u,\"vbat_load\":%u,\"vsys_load\":%u,"
             "\"bq_fault0\":%u,\"bq_fault1\":%u,"
             /* Remote config in effect (com-0.35, DOWNLINK.md). These are the
              * values the sleep after this session will use: the ack. */
             "\"cfg_ver\":%lu,\"sample_s\":%lu,\"upload_s\":%lu",
             res->cell_rssi_dbm, res->wifi_rssi_dbm, transport,
             res->cell_reg_stat, (unsigned long)flashlog_pending(), ctx->boot_id,
             ctx->reset_reason, ctx->wake_reason ? ctx->wake_reason : "unknown",
             ctx->boot_count, ctx->wake_count,
             ctx->crash_count, ctx->vbat_mv,
             ctx->sun_hours, ctx->voc_max_mv,
             /* -1 when the health read itself failed, which is itself the
              * datum: it separates "the module restarted" from "we never
              * reached the module at all". */
             ctx->uss_health_valid ? (int) ctx->uss_rst_cause   : -1,
             ctx->uss_health_valid ? (int) ctx->uss_lh_starts   : -1,
             ctx->uss_health_valid ? (int) ctx->uss_lh_uptime_s : -1,
             (int) ctx->uss_preset,
             (unsigned long)res->t_modem_ms, (unsigned long)res->t_reg_ms,
             (unsigned long)res->t_ppp_ms,   (unsigned long)res->t_sntp_ms,
             (unsigned long)res->t_mqtt_ms,  (unsigned long)res->t_drain_ms,
             (unsigned long)res->t_pub_max_ms, res->n_batches,
             (unsigned long)res->sent, res->drain_broke ? 1u : 0u,
             res->vbat_pre_mv, res->vbat_load_mv, res->vsys_load_mv,
             res->fault0, res->fault1,
             (unsigned long)devcfg_ver(), (unsigned long)devcfg_sample_s(),
             (unsigned long)devcfg_upload_s());
    /* Only while the last received payload was rejected; absent otherwise. */
    if (devcfg_err()) {
        size_t l = strlen(vals);
        snprintf(vals + l, sizeof(vals) - l, ",\"cfg_err\":\"%s\"", devcfg_err());
    }
    /* Only after a failed OTA attempt (this session, or a rollback found at
     * boot); "fw" above is the acknowledgement of a successful one. */
    if (devcfg_fw_err()) {
        size_t l = strlen(vals);
        snprintf(vals + l, sizeof(vals) - l, ",\"fw_err\":\"%s\",\"fw_err_ver\":\"%s\"",
                 devcfg_fw_err(), devcfg_fw_err_ver() ? devcfg_fw_err_ver() : "?");
    }
    if (now_ms > 0)
        snprintf(s_json, sizeof(s_json), "{\"ts\":%lld,\"values\":{%s}}",
                 (long long)now_ms, vals);
    else
        snprintf(s_json, sizeof(s_json), "{%s}", vals);
    publish_resilient(s_json);
}

/* Parse an RFC 7231 Date header ("Tue, 11 Aug 2026 16:29:42 GMT") to epoch. */
static time_t parse_http_date(const char *s)
{
    static const char *mon = "JanFebMarAprMayJunJulAugSepOctNovDec";
    int d, y, hh, mm, ss;
    char mstr[4] = { 0 };
    const char *comma = strchr(s, ',');
    if (!comma) return 0;
    if (sscanf(comma + 1, " %d %3s %d %d:%d:%d", &d, mstr, &y, &hh, &mm, &ss) != 6)
        return 0;
    const char *mp = strstr(mon, mstr);
    if (!mp) return 0;
    int m = (int)(mp - mon) / 3;   /* 0-based month */
    /* days-from-civil (Howard Hinnant), valid for y >= 1970 */
    int yy = y - (m < 2);
    int era = yy / 400;
    int yoe = yy - era * 400;
    int doy = (153 * (m + (m > 1 ? -2 : 10)) + 2) / 5 + d - 1;
    int doe = yoe * 365 + yoe / 4 - yoe / 100 + doy;
    long days = (long)era * 146097 + doe - 719468;
    return (time_t)days * 86400 + hh * 3600 + mm * 60 + ss;
}

/* Fetch trusted time from the TB server's HTTPS Date header. The carrier can
 * intercept UDP NTP; it cannot rewrite a header inside our TLS session. */
static char s_date_hdr[64];

static esp_err_t http_evt(esp_http_client_event_t *e)
{
    if (e->event_id == HTTP_EVENT_ON_HEADER &&
        strcasecmp(e->header_key, "Date") == 0) {
        strncpy(s_date_hdr, e->header_value, sizeof(s_date_hdr) - 1);
    }
    return ESP_OK;
}

static time_t https_trusted_time(void)
{
    s_date_hdr[0] = 0;
    esp_http_client_config_t cfg = {
        .url = "https://eu.thingsboard.cloud/api/v1/ping",
        .cert_pem = isrg_root_pem,
        .timeout_ms = 10000,
        .event_handler = http_evt,
    };
    esp_http_client_handle_t c = esp_http_client_init(&cfg);
    if (!c) return 0;
    esp_http_client_perform(c);   /* any status is fine; we want the header */
    esp_http_client_cleanup(c);
    return s_date_hdr[0] ? parse_http_date(s_date_hdr) : 0;
}

/* Re-sync the clock only when it is actually stale.
 *
 * sntp_sync() costs 5-7 s with the modem powered, and it ran on EVERY session
 * -- including a retry 30 minutes after the last successful sync, and the
 * second and third sessions of the same upload cycle. The RTC keeps time
 * across deep sleep, so the useful rate is daily, not hourly.
 *
 * Still forced whenever the clock is INVALID: record timestamps depend on it,
 * and record_ts_ms() falls back to reconstructing them from uptime, which is
 * exactly the case the cross-check in sntp_sync() exists to catch. */
#define CLOCK_RESYNC_S  (12 * 3600)
RTC_DATA_ATTR static int64_t s_last_clock_sync;

static void sntp_sync(void);

static void maybe_sntp_sync(void)
{
    if (clock_valid() && s_last_clock_sync &&
        llabs((long long)(time(NULL) - s_last_clock_sync)) < CLOCK_RESYNC_S) {
        ESP_LOGI(TAG, "clock fresh (%lld s old) -- skipping sync",
                 (long long)(time(NULL) - s_last_clock_sync));
        return;
    }
    sntp_sync();
    if (clock_valid()) s_last_clock_sync = time(NULL);
}

static void sntp_sync(void)
{
    esp_sntp_config_t cfg = ESP_NETIF_SNTP_DEFAULT_CONFIG_MULTIPLE(
        2, ESP_SNTP_SERVER_LIST("time.google.com", "pool.ntp.org"));
    if (esp_netif_sntp_init(&cfg) == ESP_OK) {
        esp_netif_sntp_sync_wait(pdMS_TO_TICKS(10000));
        esp_netif_sntp_deinit();
    }
    time_t sntp_t = clock_valid() ? time(NULL) : 0;

    /* Cross-check against TLS-protected HTTP time; on disagreement > 2 min the
     * HTTPS source wins (observed 2026-08-11: cellular-synced clock ran ~20-30
     * min fast -- consistent with carrier NTP interception). */
    time_t http_t = https_trusted_time();
    ESP_LOGI(TAG, "clock: sntp=%lld http=%lld (delta %lld s)",
             (long long)sntp_t, (long long)http_t,
             (long long)(sntp_t && http_t ? sntp_t - http_t : 0));
    if (http_t >= CLOCK_MIN && http_t < CLOCK_MAX) {
        if (!sntp_t || llabs((long long)(sntp_t - http_t)) > 120) {
            struct timeval tv = { .tv_sec = http_t };
            settimeofday(&tv, NULL);
            ESP_LOGW(TAG, "clock set from HTTPS Date (SNTP off by %lld s or absent)",
                     sntp_t ? (long long)(sntp_t - http_t) : 0);
        }
    }
    if (clock_valid()) {
        time_t now = time(NULL);
        ESP_LOGI(TAG, "clock now (UTC): %s", ctime(&now));
    }
}

/* ===================== cellular: esp_modem PPP ===================== */

static void on_ip_event(void *arg, esp_event_base_t base, int32_t id, void *data)
{
    if (id == IP_EVENT_PPP_GOT_IP || id == IP_EVENT_STA_GOT_IP)
        xEventGroupSetBits(s_ev, EV_IP_UP);
}

static void modem_rail(bool on)
{
    gpio_set_level(ECO_PIN_MODEM_PWR_EN, on ? 1 : 0);
}

static void pwrkey_pulse(uint32_t ms)
{
    gpio_set_level(ECO_PIN_MODEM_PWRKEY, 1);
    vTaskDelay(pdMS_TO_TICKS(100));
    gpio_set_level(ECO_PIN_MODEM_PWRKEY, 0);   /* wait -- inverter: HIGH=asserted */
    vTaskDelay(pdMS_TO_TICKS(ms));
    gpio_set_level(ECO_PIN_MODEM_PWRKEY, 1);
}

/* Wait for EPS registration (+CEREG stat 1/5) with no-signal fail-fast.
 * Returns final stat; fills rssi. */
static uint8_t wait_registration(esp_modem_dce_t *dce, uint32_t timeout_s,
                                 int *rssi_dbm)
{
    uint8_t stat = 0;
    int64_t t0 = esp_timer_get_time();
    bool saw_signal = false;
    char resp[128];

    while ((esp_timer_get_time() - t0) < (int64_t)timeout_s * 1000000) {
        esp_task_wdt_reset();

        int rssi = 99, ber = 0;
        if (esp_modem_get_signal_quality(dce, &rssi, &ber) == ESP_OK && rssi != 99) {
            saw_signal = true;
            *rssi_dbm = -113 + 2 * rssi;
        }
        if (!saw_signal &&
            (esp_timer_get_time() - t0) > (int64_t)NO_SIGNAL_FAILFAST_S * 1000000) {
            ESP_LOGW(TAG, "no signal after %d s -- fail fast", NO_SIGNAL_FAILFAST_S);
            return 0;
        }

        if (esp_modem_at(dce, "AT+CEREG?", resp, 2000) == ESP_OK) {
            char *p = strstr(resp, "+CEREG:");
            int n = 0, st = 0;
            if (p && sscanf(p, "+CEREG: %d,%d", &n, &st) == 2) {
                stat = (uint8_t)st;
                if (st == 1 || st == 5) return stat;
            }
        }
        vTaskDelay(pdMS_TO_TICKS(2000));
    }
    return stat;
}

static bool cell_session(const uplink_ctx_t *ctx, uplink_result_t *res)
{
    /* Baseline with the modem still OFF, so the mid-drain sample has something
     * to be a drop FROM. */
    res->vbat_pre_mv = bq_vbat_mv();

    /* Power sequencing per the proven Arduino driver: rail, settle, PWRKEY. */
    s_sess_t0 = esp_timer_get_time();
    modem_rail(true);
    vTaskDelay(pdMS_TO_TICKS(200));
    pwrkey_pulse(600);

    esp_modem_dce_config_t dce_cfg = ESP_MODEM_DCE_DEFAULT_CONFIG(SIM_APN);
    esp_modem_dte_config_t dte_cfg = ESP_MODEM_DTE_DEFAULT_CONFIG();
    dte_cfg.uart_config.tx_io_num = MODEM_UART_TX;
    dte_cfg.uart_config.rx_io_num = MODEM_UART_RX;
    dte_cfg.uart_config.baud_rate = MODEM_BAUD_START;

    esp_netif_config_t ppp_cfg = ESP_NETIF_DEFAULT_PPP();
    esp_netif_t *netif = esp_netif_new(&ppp_cfg);
    esp_modem_dce_t *dce = esp_modem_new_dev(ESP_MODEM_DCE_SIM7600,   /* A76xx AT set */
                                             &dte_cfg, &dce_cfg, netif);
    bool ok = false;
    if (!dce) { ESP_LOGE(TAG, "esp_modem init failed"); goto out_netif; }

    /* POLL for the modem instead of sleeping a flat 8 s.
     *
     * The old code waited 8 x 1000 ms unconditionally because "A7672 UART ready
     * ~8 s after PWRKEY", then synced once. Measured 2026-09-21: that sleep was
     * 8.9 s of a ~60 s session -- the single largest fixed cost, and the modem
     * is powered for every millisecond of it. Polling returns as soon as it
     * actually answers and keeps the same worst case.
     *
     * Creating the DCE first is safe: esp_modem_new_dev only brings up our UART
     * and the PPP netif, it does not talk to the modem. An AT sent too early
     * just fails and we try again. */
    bool synced = false;
    for (uint32_t waited = 0; waited < MODEM_READY_TO_MS; waited += 250) {
        esp_task_wdt_reset();
        if (esp_modem_sync(dce) == ESP_OK) { synced = true; break; }
        vTaskDelay(pdMS_TO_TICKS(250));
    }
    if (!synced) {
        ESP_LOGW(TAG, "modem does not answer AT after %d ms", MODEM_READY_TO_MS);
        goto out;
    }
    res->t_modem_ms = sess_ms();
    ESP_LOGI(TAG, "modem answered AT at %lu ms", (unsigned long)res->t_modem_ms);

    /* Step the link up. Both ends have to move and the modem goes first: once
     * AT+IPR lands, the modem is no longer listening at the old rate, so our
     * UART must follow immediately. The re-sync afterwards is the proof -- if
     * it fails we back out to MODEM_BAUD_START rather than spending the rest of
     * the session talking into a mismatched link. */
    if (MODEM_BAUD_FAST != MODEM_BAUD_START &&
        esp_modem_set_baud(dce, MODEM_BAUD_FAST) == ESP_OK) {
        vTaskDelay(pdMS_TO_TICKS(50));
        uart_set_baudrate(UART_NUM_1, MODEM_BAUD_FAST);
        vTaskDelay(pdMS_TO_TICKS(50));
        if (esp_modem_sync(dce) == ESP_OK) {
            ESP_LOGI(TAG, "link at %d baud", MODEM_BAUD_FAST);
        } else {
            ESP_LOGW(TAG, "%d baud did not stick -- back to %d",
                     MODEM_BAUD_FAST, MODEM_BAUD_START);
            uart_set_baudrate(UART_NUM_1, MODEM_BAUD_START);
            vTaskDelay(pdMS_TO_TICKS(50));
            (void) esp_modem_sync(dce);
        }
    }

    res->cell_reg_stat = wait_registration(
        dce, ctx->deep_search ? ATTACH_DEEP_S : ATTACH_TIMEOUT_S,
        &res->cell_rssi_dbm);
    if (res->cell_reg_stat != 1 && res->cell_reg_stat != 5) {
        ESP_LOGW(TAG, "not registered (CEREG stat %u, %d dBm)",
                 res->cell_reg_stat, res->cell_rssi_dbm);
        goto out;
    }
    res->t_reg_ms = sess_ms();
    /* The registration poll reads +CSQ before +CEREG, and a fast attach
     * answers "registered" on the first pass while +CSQ is still 99 ("not
     * known"), so rssi_dbm stayed 0 in most sessions since idf-0.28. Now that
     * we are registered the modem has a measurement within a second or so;
     * this is the last chance before PPP takes the AT channel. */
    for (int i = 0; i < 5 && res->cell_rssi_dbm == 0; i++) {
        int rssi = 99, ber = 0;
        vTaskDelay(pdMS_TO_TICKS(400));
        if (esp_modem_get_signal_quality(dce, &rssi, &ber) == ESP_OK && rssi != 99)
            res->cell_rssi_dbm = -113 + 2 * rssi;
    }
    ESP_LOGI(TAG, "registered (stat %u, %d dBm) at %lu ms",
             res->cell_reg_stat, res->cell_rssi_dbm,
             (unsigned long)res->t_reg_ms);

    xEventGroupClearBits(s_ev, EV_IP_UP);
    if (esp_modem_set_mode(dce, ESP_MODEM_MODE_DATA) != ESP_OK) {
        ESP_LOGW(TAG, "PPP mode switch failed");
        goto out;
    }
    if (!(xEventGroupWaitBits(s_ev, EV_IP_UP, pdTRUE, pdFALSE,
                              pdMS_TO_TICKS(30000)) & EV_IP_UP)) {
        ESP_LOGW(TAG, "PPP: no IP within 30 s");
        goto out;
    }
    res->t_ppp_ms = sess_ms();
    ESP_LOGI(TAG, "PPP up at %lu ms", (unsigned long)res->t_ppp_ms);

    maybe_sntp_sync();
    res->t_sntp_ms = sess_ms();

    if (mqtt_up()) {
        res->t_mqtt_ms = sess_ms();
        config_fetch();
        uint32_t sent = drain(res);
        res->t_drain_ms = sess_ms();
        res->sent += sent;
        res->sent ? (res->any_success = true) : 0;
        ota_attempt(ctx, res);
        /* AFTER the drain timing is captured, so the status record carries this
         * session's own numbers rather than the previous one's. */
        send_status(ctx, res);
        ok = sent > 0 || flashlog_pending() == 0;
    }
    mqtt_down();

out:
    /* Teardown measured 18.5 s on 2026-09-21 -- as expensive as a failed drain,
     * on a session that sent nothing, and nobody knows which call it is. Stamp
     * each one rather than guess. */
    {
        uint32_t t_a = sess_ms();
        if (dce) esp_modem_destroy(dce);
        uint32_t t_b = sess_ms();
        if (netif) esp_netif_destroy(netif);
        uint32_t t_c = sess_ms();
        ESP_LOGW(TAG, "teardown: mqtt_down->%lu, modem_destroy %lu ms, "
                      "netif_destroy %lu ms",
                 (unsigned long)t_a, (unsigned long)(t_b - t_a),
                 (unsigned long)(t_c - t_b));
        goto rail_off;
    }
out_netif:
    if (netif) esp_netif_destroy(netif);
rail_off:;
    /* Rail hard-off is the recovery guarantee -- a wedged modem never survives
     * to the next attempt (the bucket fleet's dead-end, solved in hardware). */
    modem_rail(false);
    res->t_total_ms = sess_ms();
    /* One line that accounts for the whole session. Phase cost is the gap
     * between consecutive columns; the modem is powered for all of it. */
    ESP_LOGW(TAG, "session: at=%lu reg=%lu ppp=%lu sntp=%lu mqtt=%lu drain=%lu "
                  "total=%lu ms | %u batches, slowest %lu ms, %lu sent%s",
             (unsigned long)res->t_modem_ms, (unsigned long)res->t_reg_ms,
             (unsigned long)res->t_ppp_ms,   (unsigned long)res->t_sntp_ms,
             (unsigned long)res->t_mqtt_ms,  (unsigned long)res->t_drain_ms,
             (unsigned long)res->t_total_ms, res->n_batches,
             (unsigned long)res->t_pub_max_ms, (unsigned long)res->sent,
             res->drain_broke ? ", DRAIN BROKE" : "");
    return ok;
}

/* ===================== WiFi backup ===================== */

#ifdef WIFI_SSID
static bool wifi_session(const uplink_ctx_t *ctx, uplink_result_t *res)
{
    esp_netif_create_default_wifi_sta();
    wifi_init_config_t init = WIFI_INIT_CONFIG_DEFAULT();
    if (esp_wifi_init(&init) != ESP_OK) return false;

    wifi_config_t wc = { 0 };
    strncpy((char *)wc.sta.ssid, WIFI_SSID, sizeof(wc.sta.ssid) - 1);
    strncpy((char *)wc.sta.password, WIFI_PASS, sizeof(wc.sta.password) - 1);
    esp_wifi_set_mode(WIFI_MODE_STA);
    esp_wifi_set_config(WIFI_IF_STA, &wc);
    esp_wifi_set_ps(WIFI_PS_NONE);   /* modem power-save eats packets (dl-2.10) */

    bool ok = false;
    xEventGroupClearBits(s_ev, EV_IP_UP);
    if (esp_wifi_start() != ESP_OK) goto out;
    esp_wifi_connect();
    if (!(xEventGroupWaitBits(s_ev, EV_IP_UP, pdTRUE, pdFALSE,
                              pdMS_TO_TICKS(20000)) & EV_IP_UP)) {
        ESP_LOGW(TAG, "wifi: no IP within 20 s");
        goto out;
    }

    wifi_ap_record_t ap;
    if (esp_wifi_sta_get_ap_info(&ap) == ESP_OK) res->wifi_rssi_dbm = ap.rssi;
    ESP_LOGI(TAG, "wifi up (%d dBm)", res->wifi_rssi_dbm);

    maybe_sntp_sync();

    if (mqtt_up()) {
        res->used_wifi = true;
        config_fetch();
        uint32_t sent = drain(res);
        res->sent += sent;
        if (sent) res->any_success = true;
        ota_attempt(ctx, res);
        send_status(ctx, res);   /* always: health must not depend on the drain */
        ok = sent > 0 || flashlog_pending() == 0;
    }
    mqtt_down();

out:
    esp_wifi_stop();
    esp_wifi_deinit();
    return ok;
}
#endif

/* ===================== entry point ===================== */

/* Held for the duration of an uplink. The modem UART derives its baud from a
 * clock that DFS moves, and esp_modem does not take its own lock -- without
 * this the first frequency change mid-session corrupts the AT stream. Restored
 * verbatim in intent from e86c644: it shipped ALONGSIDE the PM config, so a
 * reproduction without it is not the historical firmware. It also matters for
 * the experiment itself -- an AT-stream corruption can panic the upload, and a
 * panic reboots this board, cycles the sensor rail, resets the module and
 * forces an abs-ToF re-search. That is the exact code-135 signature we are
 * using as the positive result, so leaving this out could fake one. */
static esp_pm_lock_handle_t s_pm_lock;

static void pm_hold(bool hold)
{
    if (!s_pm_lock &&
        esp_pm_lock_create(ESP_PM_NO_LIGHT_SLEEP, 0, "uplink", &s_pm_lock) != ESP_OK)
        return;
    if (hold) esp_pm_lock_acquire(s_pm_lock);
    else      esp_pm_lock_release(s_pm_lock);
}

uplink_result_t uplink_upload_all(const uplink_ctx_t *ctx)
{
    uplink_result_t res = { 0 };
    pm_hold(true);

    s_ref_uptime_s = ctx->uptime_s;
    s_ref_boot_id  = ctx->boot_id;

    if (!s_ev) {
        s_ev = xEventGroupCreate();
        esp_netif_init();
        esp_event_loop_create_default();
        esp_event_handler_register(IP_EVENT, ESP_EVENT_ANY_ID, on_ip_event, NULL);
    }

    bool input = ctx->vbat_mv == 0;   /* unknown VBAT (no BQ): don't gate */

    /* Cellular primary, battery-gated (A7672 bursts sag the pack). */
    if (!ctx->skip_cellular && (input || ctx->vbat_mv >= MODEM_MIN_VBAT_MV)) {
        cell_session(ctx, &res);
    } else if (ctx->skip_cellular) {
        ESP_LOGW(TAG, "skipping cellular (previous attempt crashed)");
    } else {
        ESP_LOGW(TAG, "VBAT %u mV below modem floor %d -- cellular skipped",
                 ctx->vbat_mv, MODEM_MIN_VBAT_MV);
    }

#ifdef WIFI_SSID
    if (flashlog_pending() > 0 && (input || ctx->vbat_mv >= WIFI_MIN_VBAT_MV))
        wifi_session(ctx, &res);
#endif

    res.all_sent = (flashlog_pending() == 0);
    ESP_LOGI(TAG, "%lu records sent%s, %lu pending",
             (unsigned long)res.sent, res.used_wifi ? " (wifi used)" : "",
             (unsigned long)flashlog_pending());
    pm_hold(false);
    return res;
}
